fhnw-sgi-ip12-22vt/ip12-22vt_flow/Docu/hardware/images/AcrylstabHalter.png

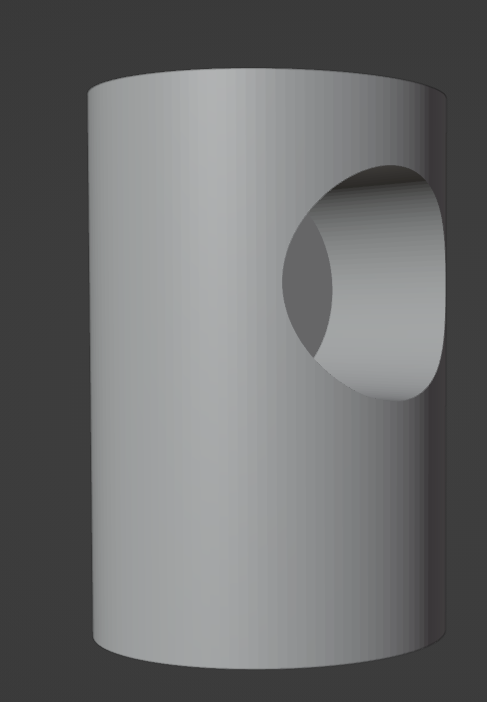
Docu/hardware/images/AcrylstabHalter.png
