fhnw-sgi-ip12-22vt/ip12-22vt_flow/Docu/hardware/images/Deckel_mit_Arrows.jpg

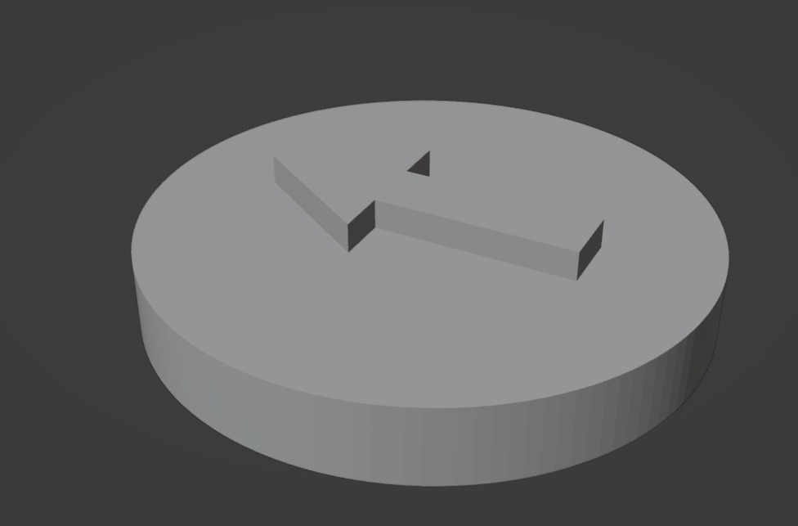
Docu/hardware/images/Deckel_mit_Arrows.jpg
