fhnw-sgi-ip12-22vt/ip12-22vt_flow/Docu/hardware/images/HyperLoopStationVar4_2.png

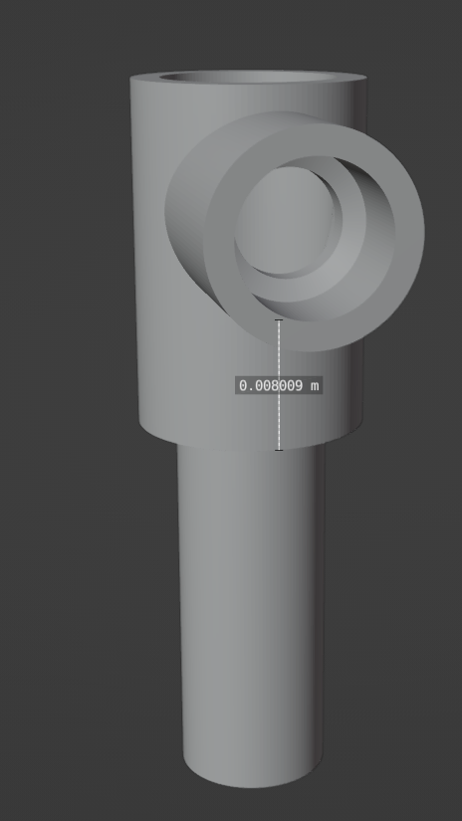
Docu/hardware/images/HyperLoopStationVar4_2.png
