fhnw-sgi-ip12-22vt/ip12-22vt_flow/Docu/hardware/images/IP12_Edge_Capacity_Number_2.jpg

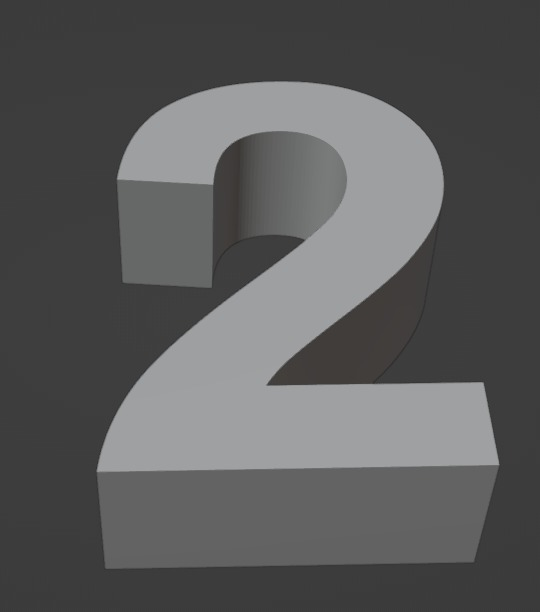
Docu/hardware/images/IP12_Edge_Capacity_Number_2.jpg
