fhnw-sgi-ip12-22vt/ip12-22vt_flow/Docu/hardware/images/ip12factory.png

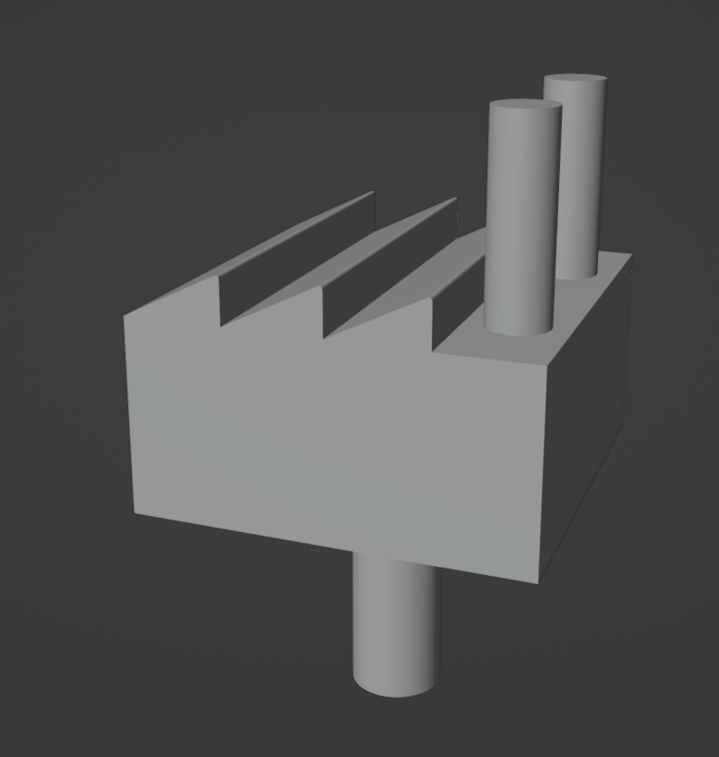
Docu/hardware/images/ip12factory.png
