fhnw-sgi-ip12-22vt/ip12-22vt_flow/Docu/hardware/images/Wasserkraftwerk14x9.png

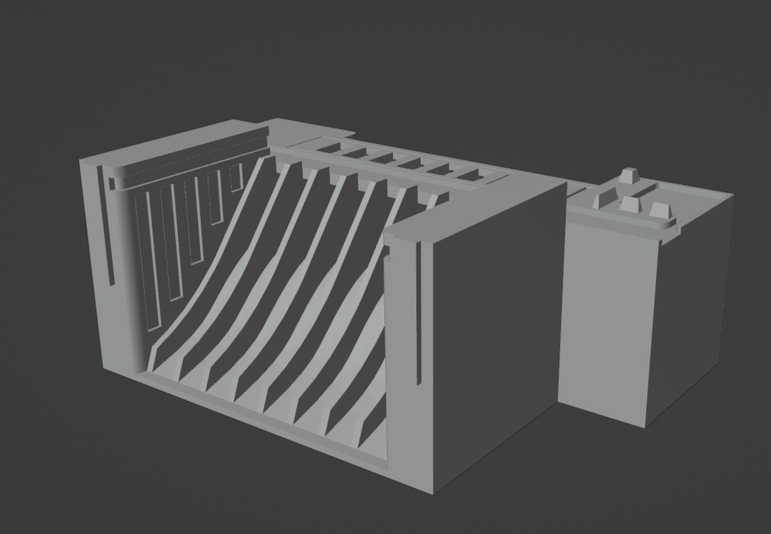
Docu/hardware/images/Wasserkraftwerk14x9.png
