fhnw-sgi-ip12-22vt/ip12-22vt_flow/Docu/hardware/images/WindkraftwerkTurbine.png

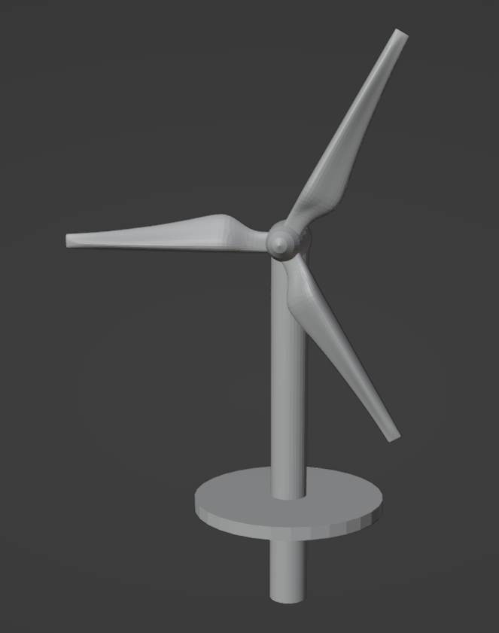
Docu/hardware/images/WindkraftwerkTurbine.png
