fhnw-sgi-ip12-22vt/ip12-22vt_flow/Docu/software(sad)/src/Default View.bmp

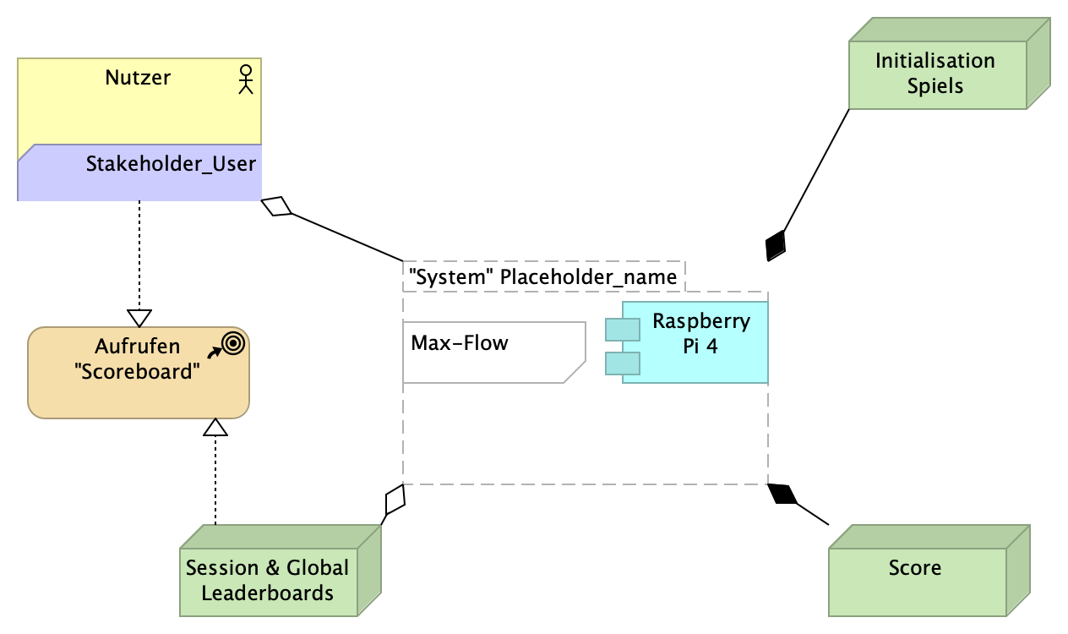
Docu/software(sad)/src/Default View.bmp
