fhnw-sgi-ip12-22vt/ip12-22vt_flow/Docu/software(sad)/src/images/Outside_Context.png

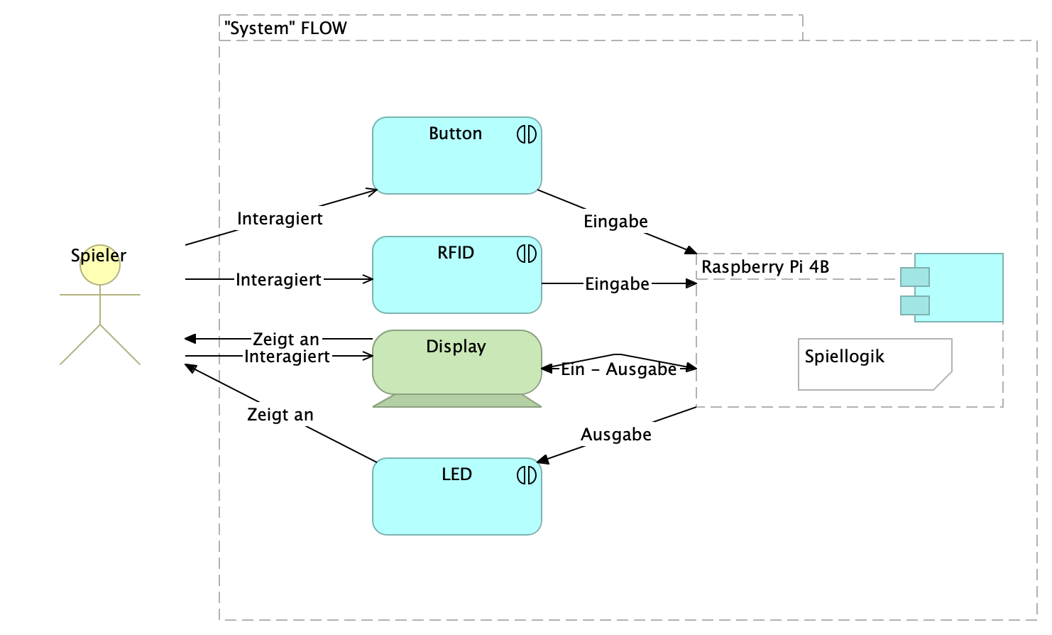
Docu/software(sad)/src/images/Outside_Context.png
