fhnw-sgi-ip12-22vt/ip12-22vt_flow/Docu/software(sad)/src/images/Outside_Template.bmp

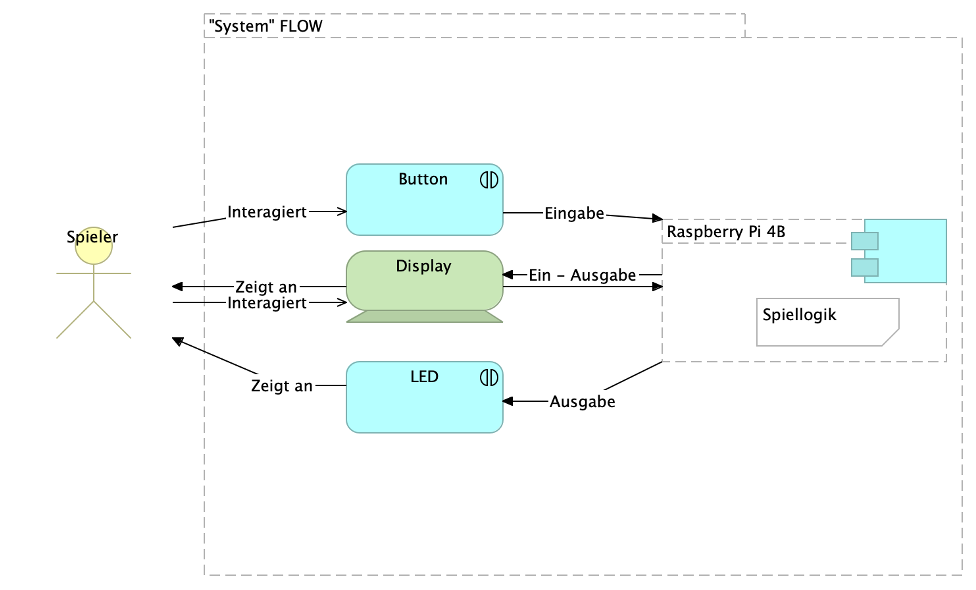
Docu/software(sad)/src/images/Outside_Template.bmp
